UdeS-GRO/S4H2019-bro-bot/image_wiki/finger_control.PNG

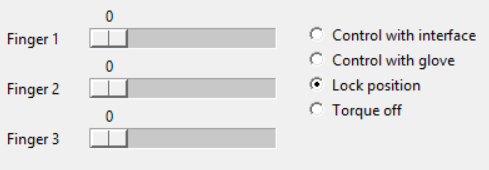
image_wiki/finger_control.PNG
