UdeS-GRO/S4H2019-bro-bot/image_wiki/gui.PNG

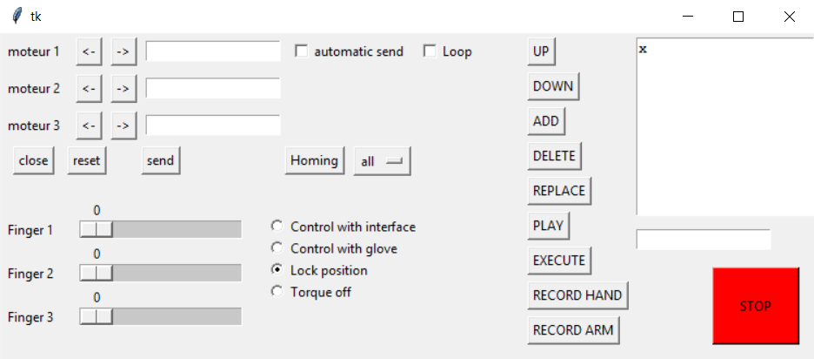
image_wiki/gui.PNG
