UdeS-GRO/S4H2019-bro-bot/Software/HandControl/HandControl.h

#pragma once
/*
	This Source Code Form is subject to the terms of the Mozilla Public
	License, v. 2.0.If a copy of the MPL was not distributed with this
	file, You can obtain one at http ://mozilla.org/MPL/2.0/.
*/


#ifndef HAND_CONTROL_H
#define HAND_CONTROL_H

#include <SPI.h>
#include <nRF24L01.h>
#include <RF24.h>
#include <Servo.h>
#include "Arduino.h"


enum ControlFingerState
{
	LOCK = 1,
	FREE,
	GLOVE,
	GUI
};

class HandControl
{
private:
	int* finger_gui_cmd_;
	int* finger_glove_cmd_;
	int nb_of_finger;
	ControlFingerState mode;
	Servo thumb;
	Servo INDEX;
	Servo middle;
	//const byte address[6] = "gant0";
	char text_radio[10] = "";
  	String finger_value_str = "";
	int flexsensorRange[2][3]= {{20,20,20},
                            	{0,0,0}};
	RF24 *radio; 
	int pin_m1 = 2;
	int pin_m2 = 3;
	int pin_m3 = 4;

public:
	/* Constructor and destructor*/
	HandControl(int number_of_fingers);
	~HandControl();

	void setMode(ControlFingerState new_mode);
	ControlFingerState getMode(void);

	// *****************************
	// **** individual function(touch a specified finger) ****
	void setFingerGuiValue(int finger_number, int new_value);
	int getFingerGuiValue(int finger_number);

	void setFingerGloveValue(int finger_number, int new_value);
	int getFingerGloveValue(int finger_number);

	// *****************************
	// **** general function(touch every finger) ****
	void attachMotor(void);
	void detachMotor(void);

	void setMotorValue(void);
	void getMotorValue(void);

	void read_radio(void);

};



#endif
